v-ivanyshyn/mqb-steering-wheel-adapter/firmwares/acc, cnl/img.png

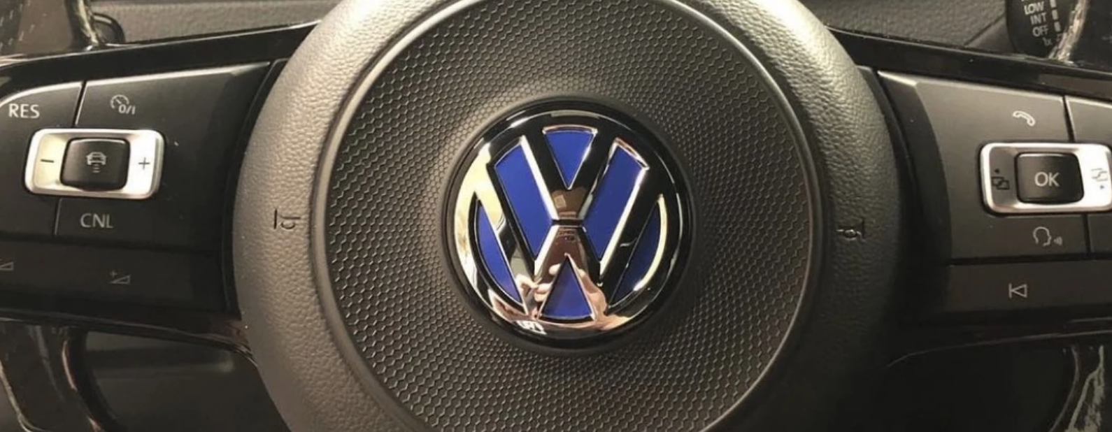
firmwares/acc, cnl/img.png
